dohn-joh/heatwave/ergogen/output/outlines/choc_pin_cutouts.dxf

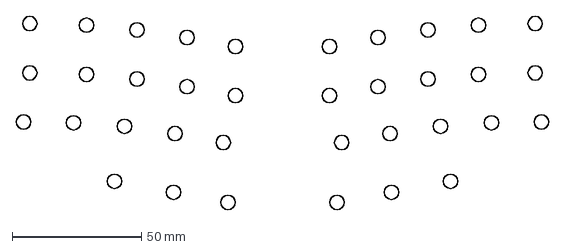
[picture p15: CAD file, 2025-04-10]
ergogen/output/outlines/choc_pin_cutouts.dxf
205.6 x 74.6 mm
