dohn-joh/heatwave/ergogen/output/outlines/switch_cutouts.dxf

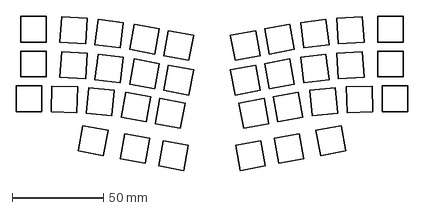
[picture p16: CAD file, 2025-04-10]
ergogen/output/outlines/switch_cutouts.dxf
214.0 x 84.2 mm
