dohn-joh/heatwave/ergogen/output/outlines/keycaps.dxf

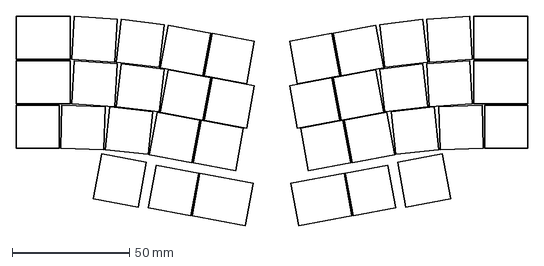
[picture p17: CAD file, 2025-04-10]
ergogen/output/outlines/keycaps.dxf
218.4 x 89.4 mm
