dohn-joh/heatwave/ergogen/output/outlines/top_case_gap.dxf

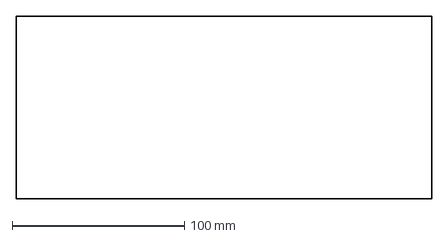
[picture p18: CAD file, 2025-04-10]
ergogen/output/outlines/top_case_gap.dxf
241.0 x 106.0 mm
