dohn-joh/heatwave/ergogen/output/outlines/top_case_outer.dxf

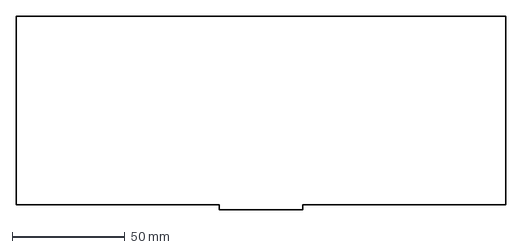
[picture p19: CAD file, 2025-04-10]
ergogen/output/outlines/top_case_outer.dxf
217.4 x 85.9 mm
