dohn-joh/heatwave/ergogen/output/outlines/test.dxf

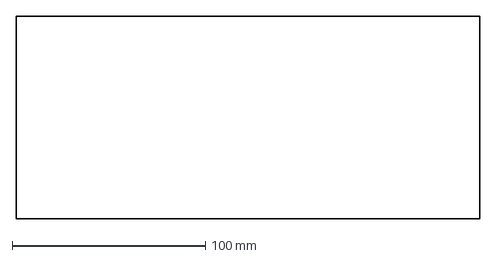
[picture p20: CAD file, 2025-04-10]
ergogen/output/outlines/test.dxf
240.0 x 105.0 mm
